AudioMorphology/ParrotRev2/Documentation/Camberwell Parrot 1820x1024 colour.png

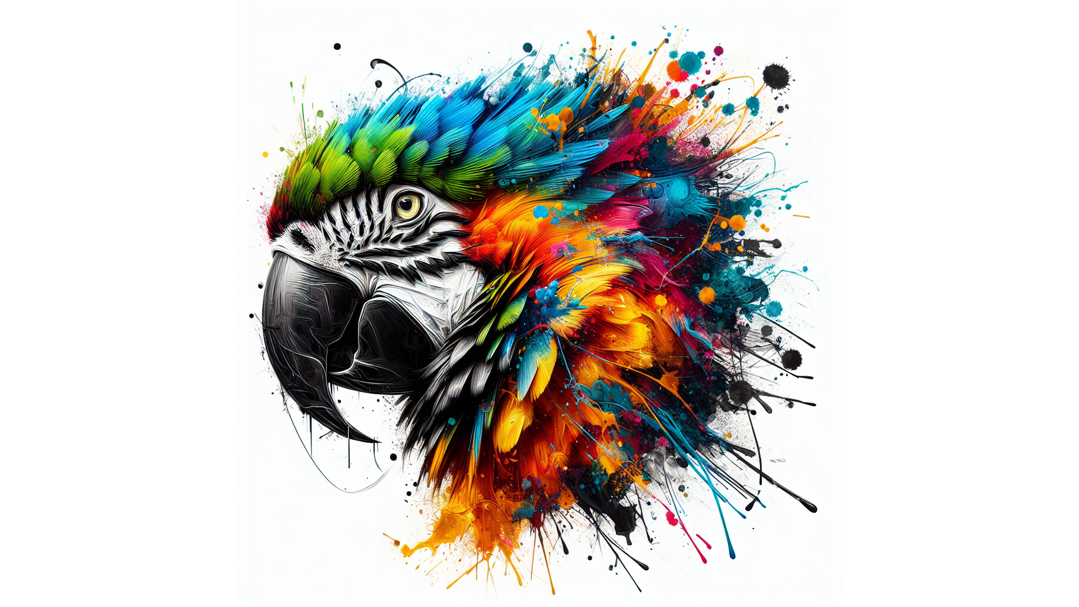
Documentation/Camberwell Parrot 1820x1024 colour.png
