AudioMorphology/ParrotRev2/Documentation/Camberwell Parrot 1820x1024 grey+text.png

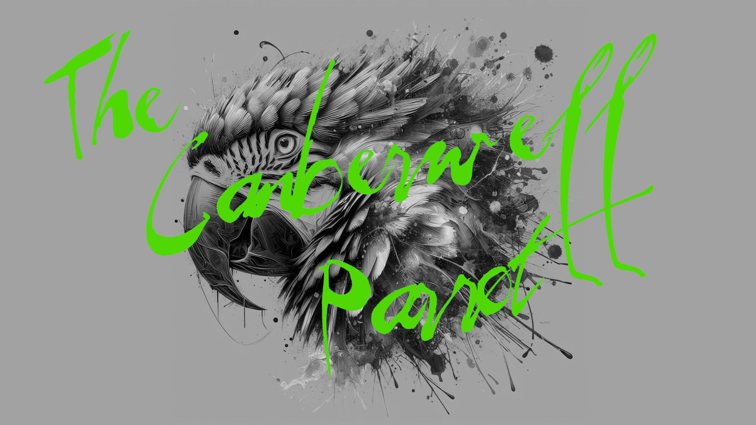
Documentation/Camberwell Parrot 1820x1024 grey+text.png
