AudioMorphology/ParrotRev2/Documentation/Camberwell Parrot 1820x1024 greyscale + rainbow text + Squirting + Blotting.png

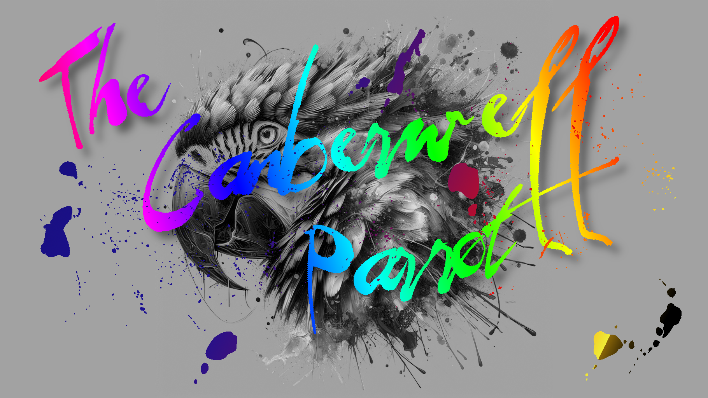
Documentation/Camberwell Parrot 1820x1024 greyscale + rainbow text + Squirting + Blotting.png
