AudioMorphology/ParrotRev2/Documentation/Camberwell Parrot v1.png

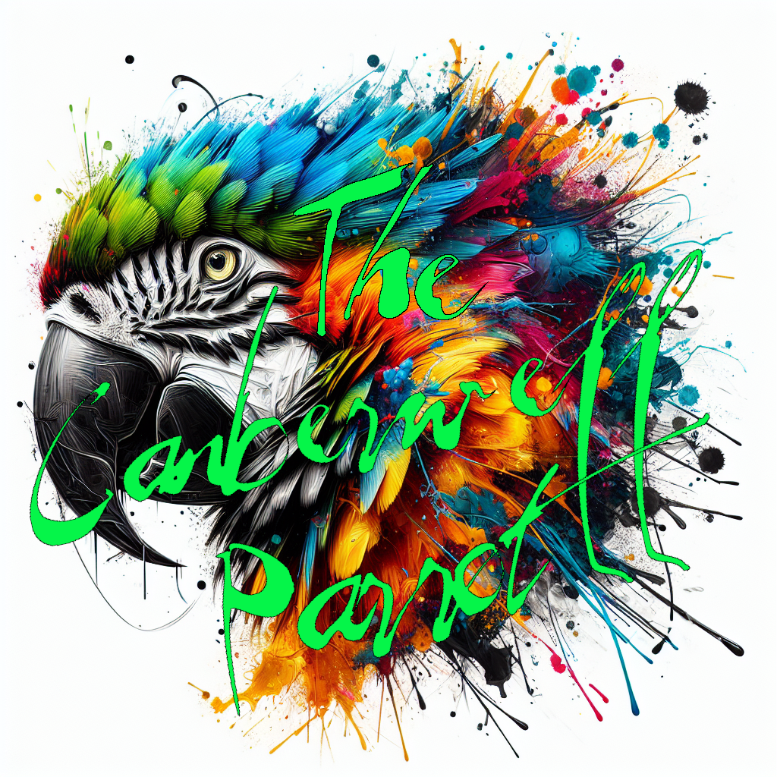
Documentation/Camberwell Parrot v1.png
