AudioMorphology/ParrotRev2/Documentation/Camberwell Parrot v2.png

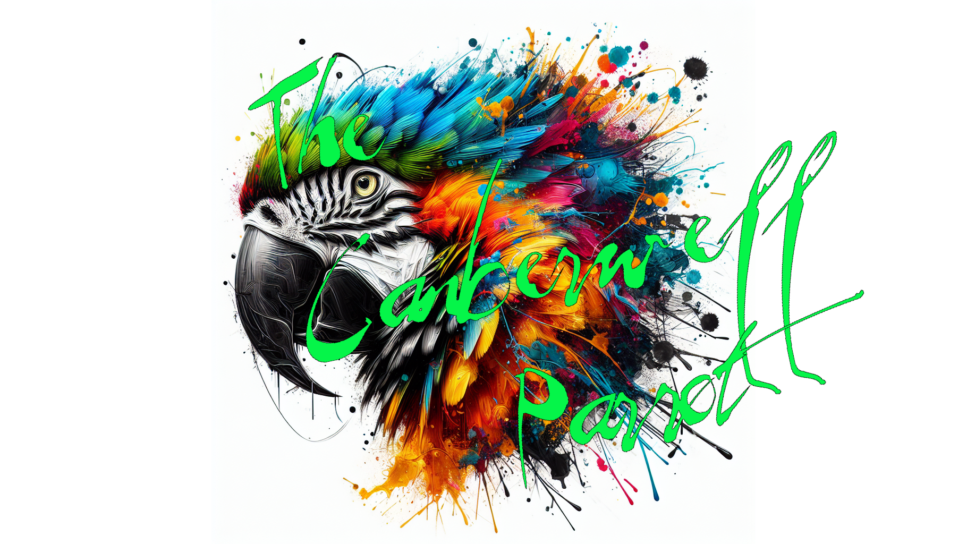
Documentation/Camberwell Parrot v2.png
