AudioMorphology/ParrotRev2/Documentation/tplImg8b8c13e680d24402b4a53ab269263721.png

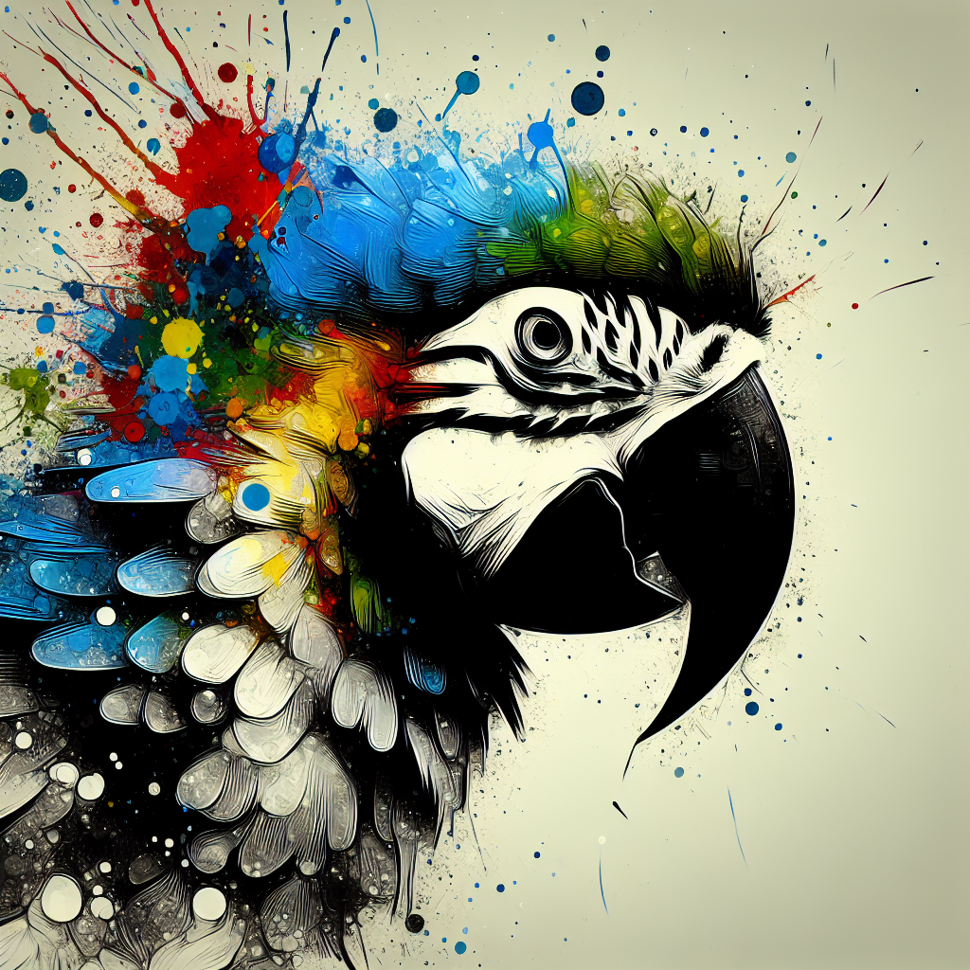
Documentation/tplImg8b8c13e680d24402b4a53ab269263721.png
