AudioMorphology/ParrotRev2/freeverb/freeverb.c

/*
** freeverb v0.1
**
** Public domain C implementation of the original freeverb, with the addition of
** support for samplerates other than 44.1khz.
**
** Original C++ version written by Jezar at Dreampoint, June 2000
*/
#include "freeverb.h"
#include <stdlib.h>

#define undenormalize(n) { if (xabs(n) < 1e-37) { (n) = 0; } }


static inline float xabs(float n) {
  return n < 0 ? -n : n;
}


static inline void zeroset(void *buf, int n) {
  while (n--) { ((char*) buf)[n] = 0; }
}


static inline float allpass_process(fv_Allpass *ap, float input) {
  float bufout = ap->buf[ap->bufidx];
  undenormalize(bufout);

  float output = -input + bufout;
  ap->buf[ap->bufidx] = input + bufout * ap->feedback;

  if (++ap->bufidx >= ap->bufsize) {
    ap->bufidx = 0;
  }

  return output;
}


static inline float comb_process(fv_Comb *cmb, float input) {
  float output = cmb->buf[cmb->bufidx];
  undenormalize(output);

  cmb->filterstore = output * cmb->damp2 + cmb->filterstore * cmb->damp1;
  undenormalize(cmb->filterstore);

  cmb->buf[cmb->bufidx] = input + cmb->filterstore * cmb->feedback;

  if (++cmb->bufidx >= cmb->bufsize) {
    cmb->bufidx = 0;
  }

  return output;
}


static inline void comb_set_damp(fv_Comb *cmb, float n) {
  cmb->damp1 = n;
  cmb->damp2 = 1.0 - n;
}


void fv_init(fv_Context *ctx) {
  zeroset(ctx, sizeof(*ctx));

  for (int i = 0; i < FV_NUMALLPASSES; i++) {
    ctx->allpassl[i].feedback = 0.5;
    ctx->allpassr[i].feedback = 0.5;
  }

  fv_set_samplerate(ctx, 48000);
  fv_set_wet(ctx, FV_INITIALWET);
  fv_set_roomsize(ctx, FV_INITIALROOM);
  fv_set_dry(ctx, FV_INITIALDRY);
  fv_set_damp(ctx, FV_INITIALDAMP);
  fv_set_width(ctx, FV_INITIALWIDTH);
}


void fv_mute(fv_Context *ctx) {
  for (int i = 0; i < FV_NUMCOMBS; i++) {
    zeroset(ctx->combl[i].buf, sizeof(ctx->combl[i].buf));
    zeroset(ctx->combr[i].buf, sizeof(ctx->combr[i].buf));
  }
  for (int i = 0; i < FV_NUMALLPASSES; i++) {
    zeroset(ctx->allpassl[i].buf, sizeof(ctx->allpassl[i].buf));
    zeroset(ctx->allpassr[i].buf, sizeof(ctx->allpassr[i].buf));
  }
}


static void update(fv_Context *ctx) {
  ctx->wet1 = ctx->wet * (ctx->width * 0.5 + 0.5);
  ctx->wet2 = ctx->wet * ((1 - ctx->width) * 0.5);

  if (ctx->mode >= FV_FREEZEMODE) {
    ctx->roomsize1 = 1;
    ctx->damp1 = 0;
    ctx->gain = FV_MUTED;

  } else {
    ctx->roomsize1 = ctx->roomsize;
    ctx->damp1 = ctx->damp;
    ctx->gain = FV_FIXEDGAIN;
  }

  for (int i = 0; i < FV_NUMCOMBS; i++) {
    ctx->combl[i].feedback = ctx->roomsize1;
    ctx->combr[i].feedback = ctx->roomsize1;
    comb_set_damp(&ctx->combl[i], ctx->damp1);
    comb_set_damp(&ctx->combr[i], ctx->damp1);
  }
}


void fv_set_samplerate(fv_Context *ctx, float value) {
  //const int combs[] = { 1116, 1188, 1277, 1356, 1422, 1491, 1557, 1617 }; //44100 version
  const int combs[] = { 1215, 1293, 1390, 1476, 1548, 1623, 1695, 1760 };   //48000 version
  //const int allpasses[] = { 556, 441, 341, 225 }; // 44100 Values
  const int allpasses[] = { 605, 480, 371, 245 }; // 48k Version
  //double multiplier = value / FV_INITIALSR;
  
  /* init comb buffers */
  for (int i = 0; i < FV_NUMCOMBS; i++) {
    ctx->combl[i].bufsize = combs[i];
    ctx->combl[i].buf = (float *)calloc(ctx->combl[i].bufsize + 1,sizeof(float));
    ctx->combr[i].bufsize = (combs[i] + FV_STEREOSPREAD);
    ctx->combr[i].buf = (float *)calloc(ctx->combr[i].bufsize + 1,sizeof(float));
  }

  /* init allpass buffers */
  for (int i = 0; i < FV_NUMALLPASSES; i++) {
    ctx->allpassl[i].bufsize = allpasses[i];
    ctx->allpassl[i].buf = (float *)calloc(ctx->allpassl[i].bufsize + 1,sizeof(float));
    ctx->allpassr[i].bufsize = (allpasses[i] + FV_STEREOSPREAD);
    ctx->allpassr[i].buf = (float *)calloc(ctx->allpassr[i].bufsize + 1,sizeof(float));
  }
}


void fv_set_mode(fv_Context *ctx, float value) {
  ctx->mode = value;
  update(ctx);
}


void fv_set_roomsize(fv_Context *ctx, float value) {
  ctx->roomsize = value * FV_SCALEROOM + FV_OFFSETROOM;
  update(ctx);
}


void fv_set_damp(fv_Context *ctx, float value) {
  ctx->damp = value * FV_SCALEDAMP;
  update(ctx);
}


void fv_set_wet(fv_Context *ctx, float value) {
  ctx->wet = value * FV_SCALEWET;
  update(ctx);
}


void fv_set_dry(fv_Context *ctx, float value) {
  ctx->dry = value * FV_SCALEDRY;
}


void fv_set_width(fv_Context *ctx, float value) {
  ctx->width = value;
  update(ctx);
}


void fv_process(fv_Context *ctx, float *buf, int n) {
  for (int i = 0; i < n; i += 2) {
    float outl = 0;
    float outr = 0;
    float input = (buf[i] + buf[i + 1]) * ctx->gain;

    /* accumulate comb filters in parallel */
    for (int i = 0; i < FV_NUMCOMBS; i++) {
      outl += comb_process(&ctx->combl[i], input);
      outr += comb_process(&ctx->combr[i], input);
    }

    /* feed through allpasses in series */
    for (int i = 0; i < FV_NUMALLPASSES; i++) {
      outl = allpass_process(&ctx->allpassl[i], outl);
      outr = allpass_process(&ctx->allpassr[i], outr);
    }

    /* replace buffer with output */
    buf[i  ] = outl * ctx->wet1 + outr * ctx->wet2 + buf[i  ] * ctx->dry;
    buf[i+1] = outr * ctx->wet1 + outl * ctx->wet2 + buf[i+1] * ctx->dry;
  }
}
